aalmiramolla/ArduBot/Doc/Imágenes/img/ArduinoBT.png

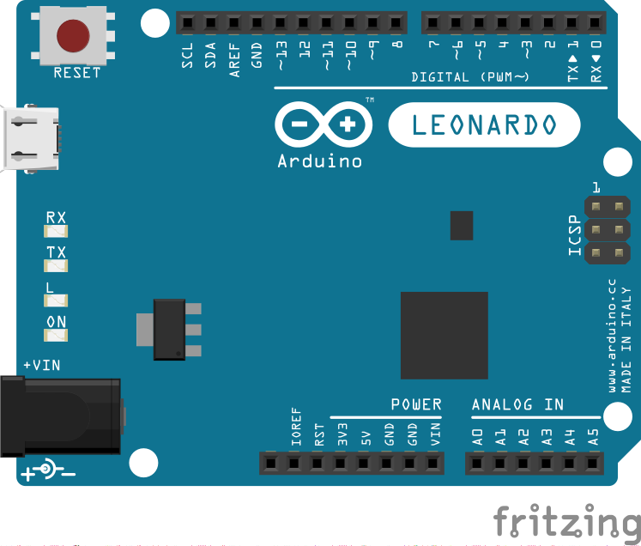
Doc/Imágenes/img/ArduinoBT.png
