aalmiramolla/ArduBot/Doc/Imágenes/img/bq.png

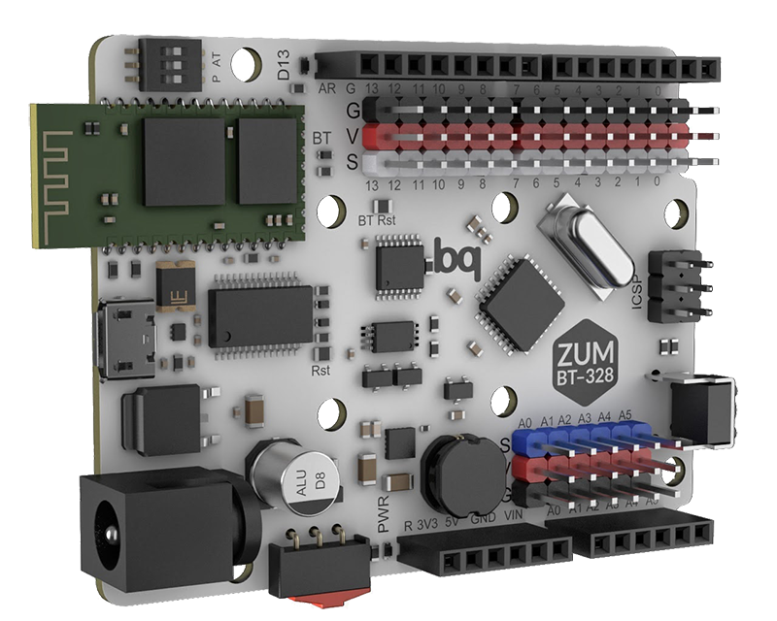
Doc/Imágenes/img/bq.png
