aalmiramolla/ArduBot/Doc/Imágenes/img/DiagramaDirectorio.png

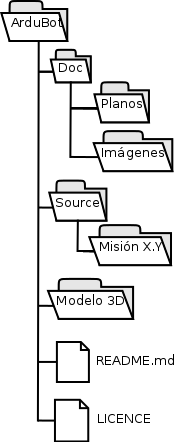
Doc/Imágenes/img/DiagramaDirectorio.png
