aalmiramolla/ArduBot/Doc/Imágenes/img/endstop.jpg

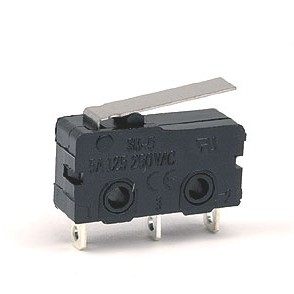
Doc/Imágenes/img/endstop.jpg
