aalmiramolla/ArduBot/Doc/Imágenes/img/endStopFunc.jpg

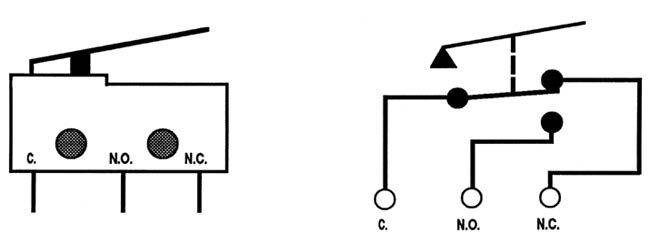
Doc/Imágenes/img/endStopFunc.jpg
