aalmiramolla/ArduBot/Doc/Imágenes/img/miniskybot.jpg

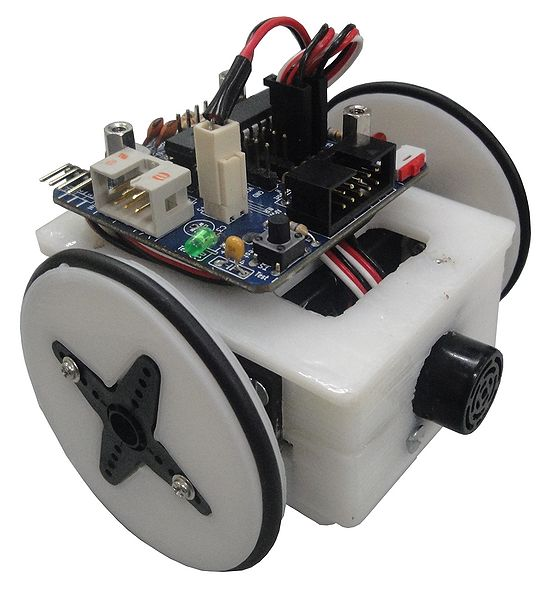
Doc/Imágenes/img/miniskybot.jpg
