aalmiramolla/ArduBot/Doc/Imágenes/img/robot_final2.jpg

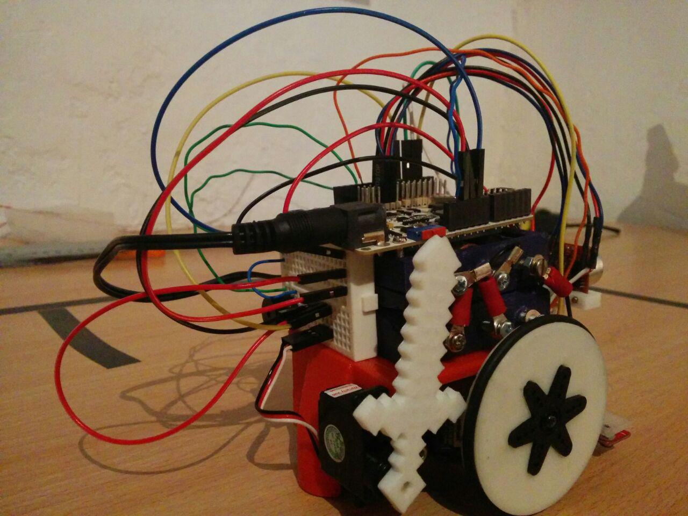
Doc/Imágenes/img/robot_final2.jpg
