aalmiramolla/ArduBot/Doc/Imágenes/img/robot_final.jpg

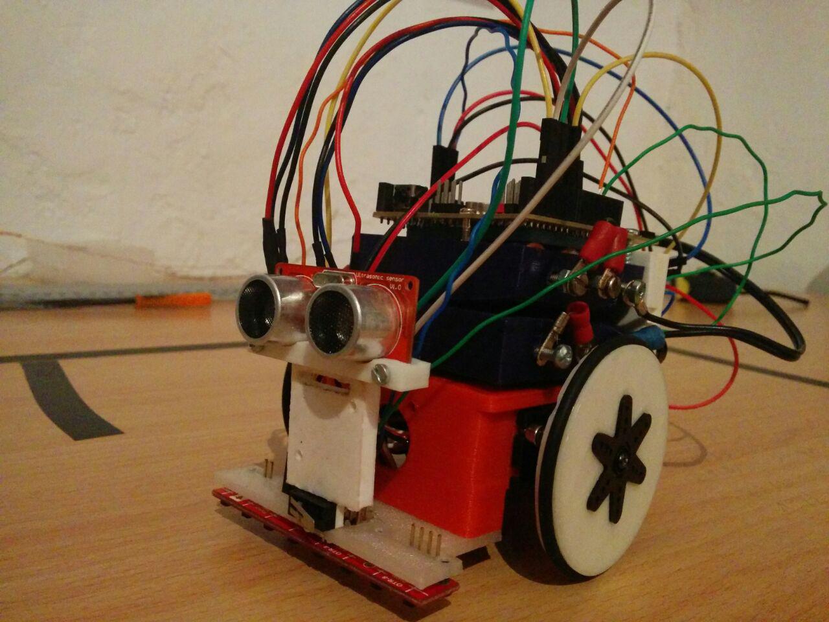
Doc/Imágenes/img/robot_final.jpg
