aalmiramolla/ArduBot/Doc/Imágenes/img/robotv1.jpg

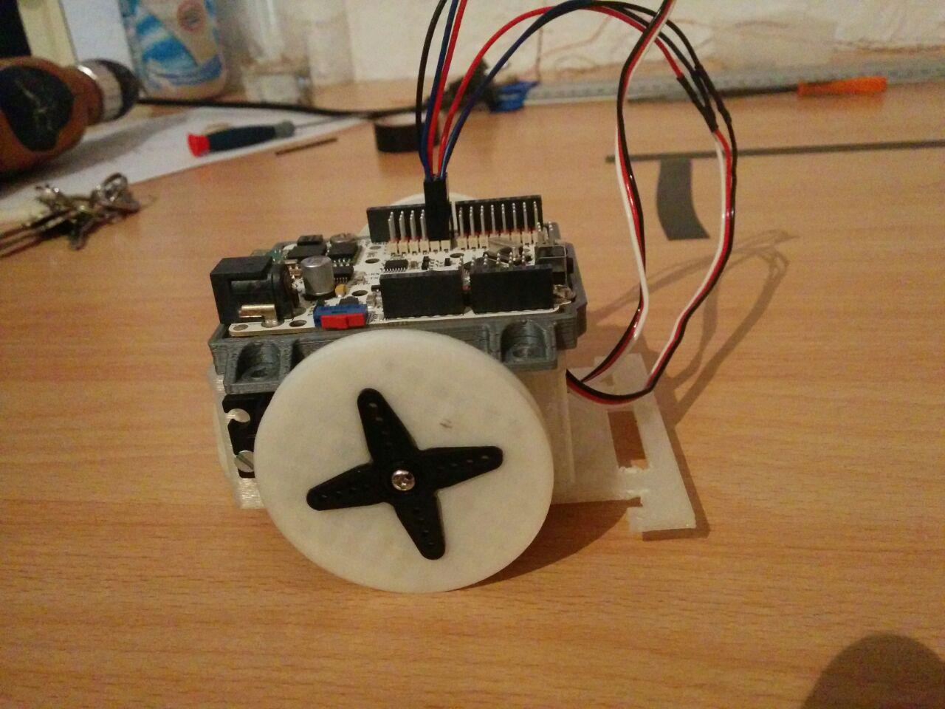
Doc/Imágenes/img/robotv1.jpg
