aalmiramolla/ArduBot/Doc/Imágenes/img/sensorluz.jpg

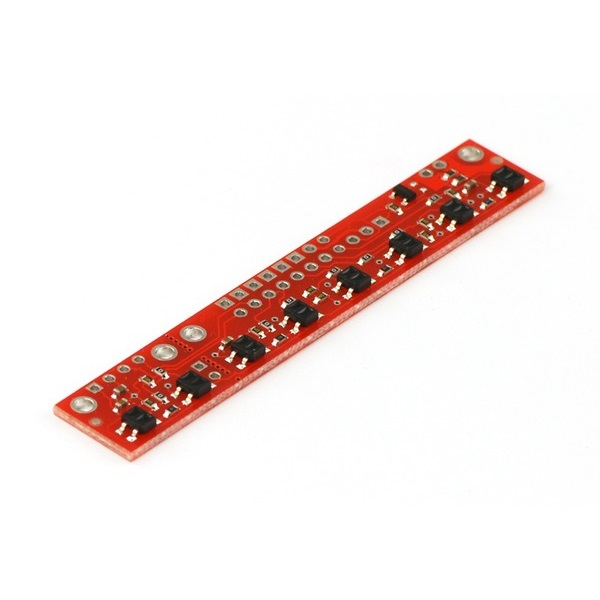
Doc/Imágenes/img/sensorluz.jpg
