aalmiramolla/ArduBot/Doc/Imágenes/img/SensorLuz.png

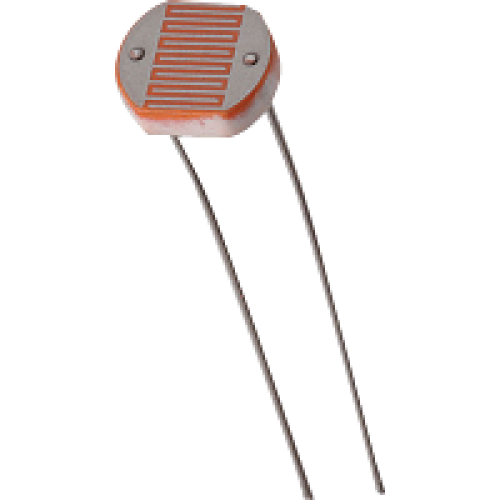
Doc/Imágenes/img/SensorLuz.png
