aalmiramolla/ArduBot/Doc/Imágenes/img/SensorReflectanciaFunc.jpg

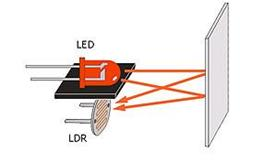
Doc/Imágenes/img/SensorReflectanciaFunc.jpg
