aalmiramolla/ArduBot/Doc/Imágenes/img/servo.jpg

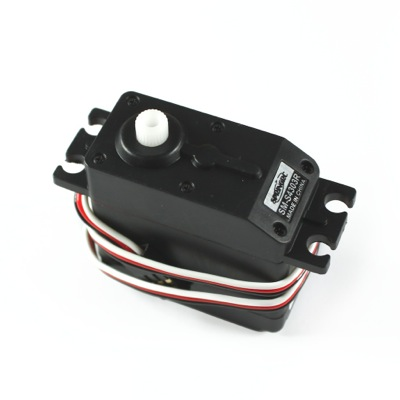
Doc/Imágenes/img/servo.jpg
