aalmiramolla/ArduBot/Doc/Imágenes/img/ServoDigital180.jpg

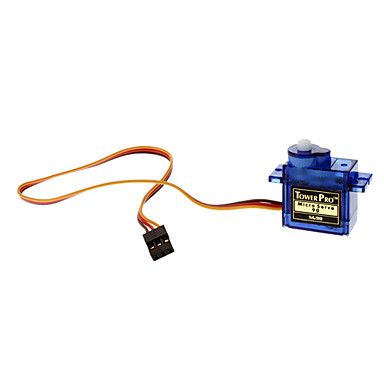
Doc/Imágenes/img/ServoDigital180.jpg
