aalmiramolla/ArduBot/Doc/Imágenes/img/sketchArduino.png

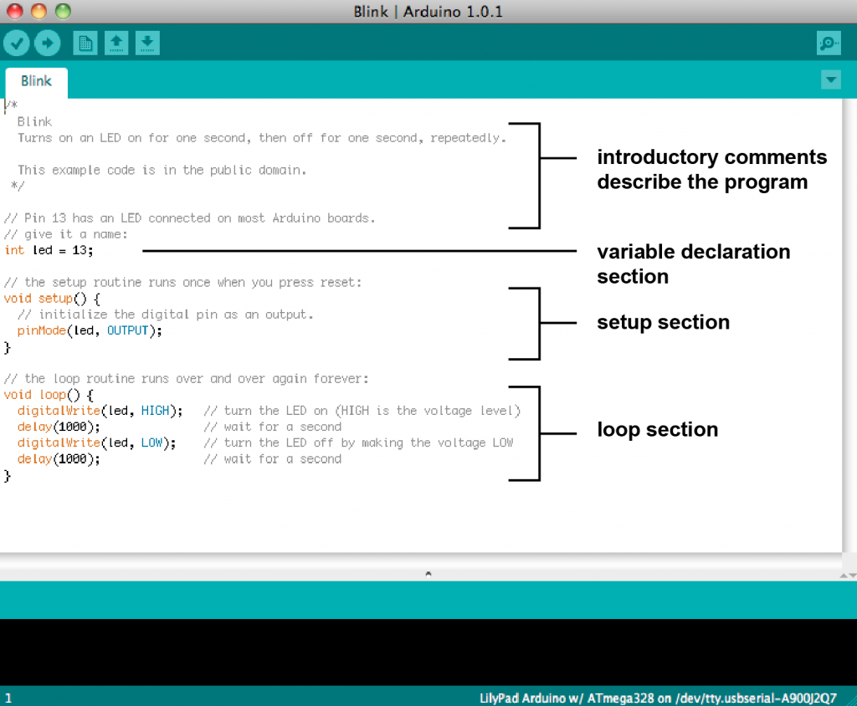
Doc/Imágenes/img/sketchArduino.png
