aalmiramolla/ArduBot/Doc/Imágenes/img/Zumbador.png

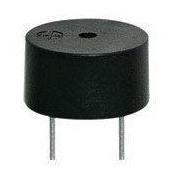
Doc/Imágenes/img/Zumbador.png
