aalmiramolla/ArduBot/Doc/Imágenes/Misiones/ImagenCirculo.png

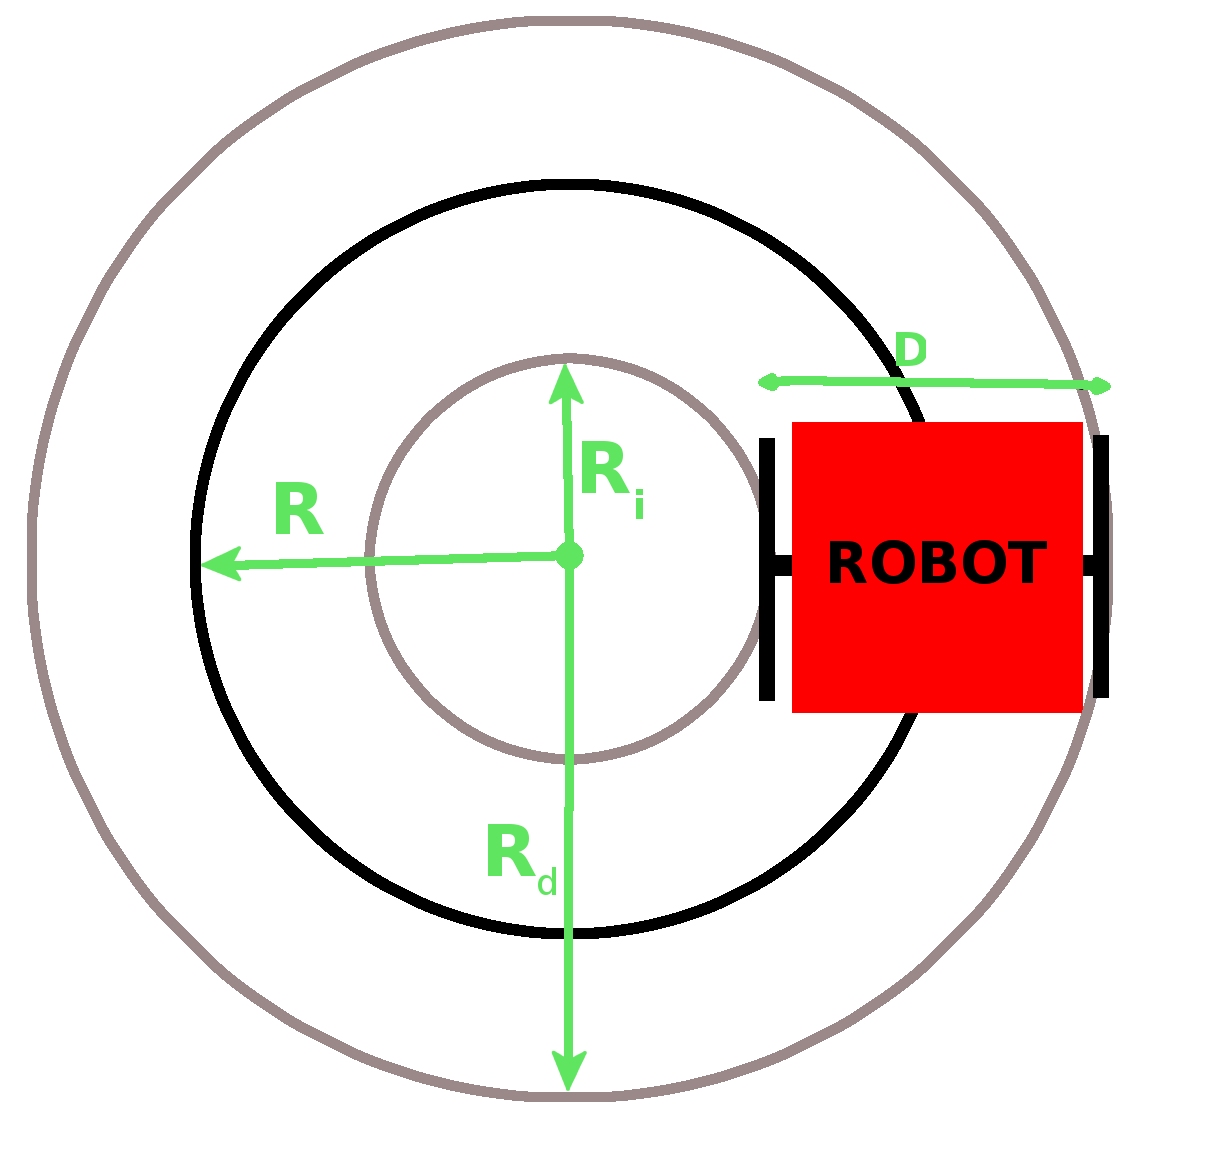
Doc/Imágenes/Misiones/ImagenCirculo.png
