aalmiramolla/ArduBot/Source/Misiones/Comunicacion/robot2.png

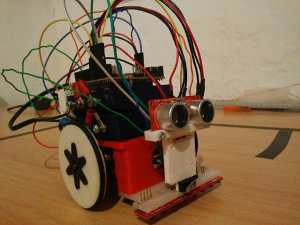
Source/Misiones/Comunicacion/robot2.png
