aalmiramolla/ArduBot/Doc/Imágenes/Montaje/MontajeUltraSonidos.jpg

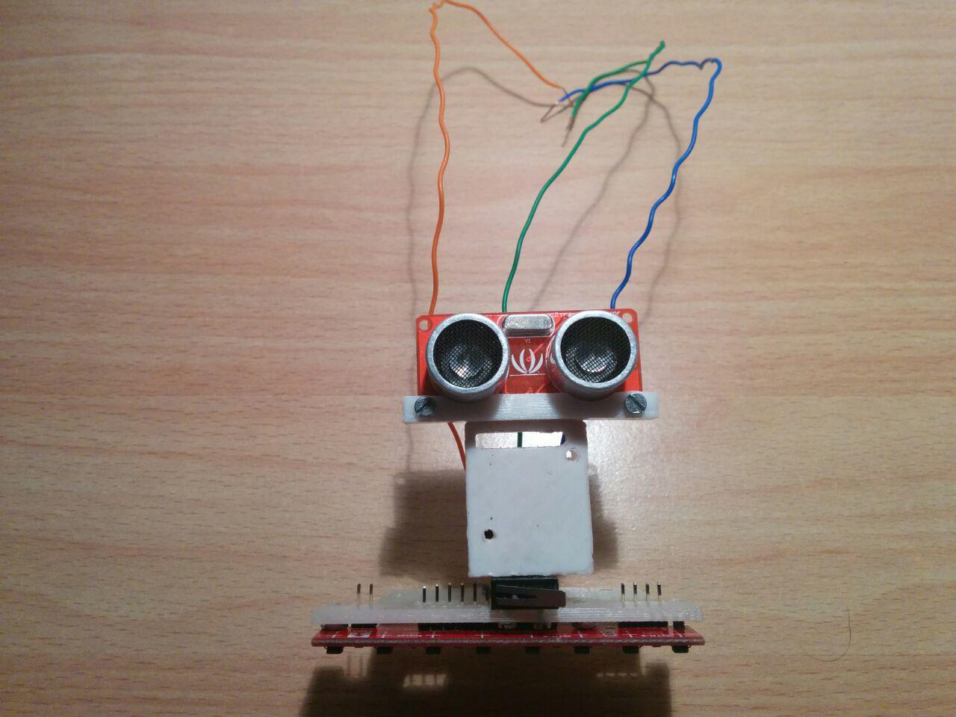
Doc/Imágenes/Montaje/MontajeUltraSonidos.jpg
