aalmiramolla/ArduBot/Doc/Imágenes/Montaje/Portapilas1.jpg

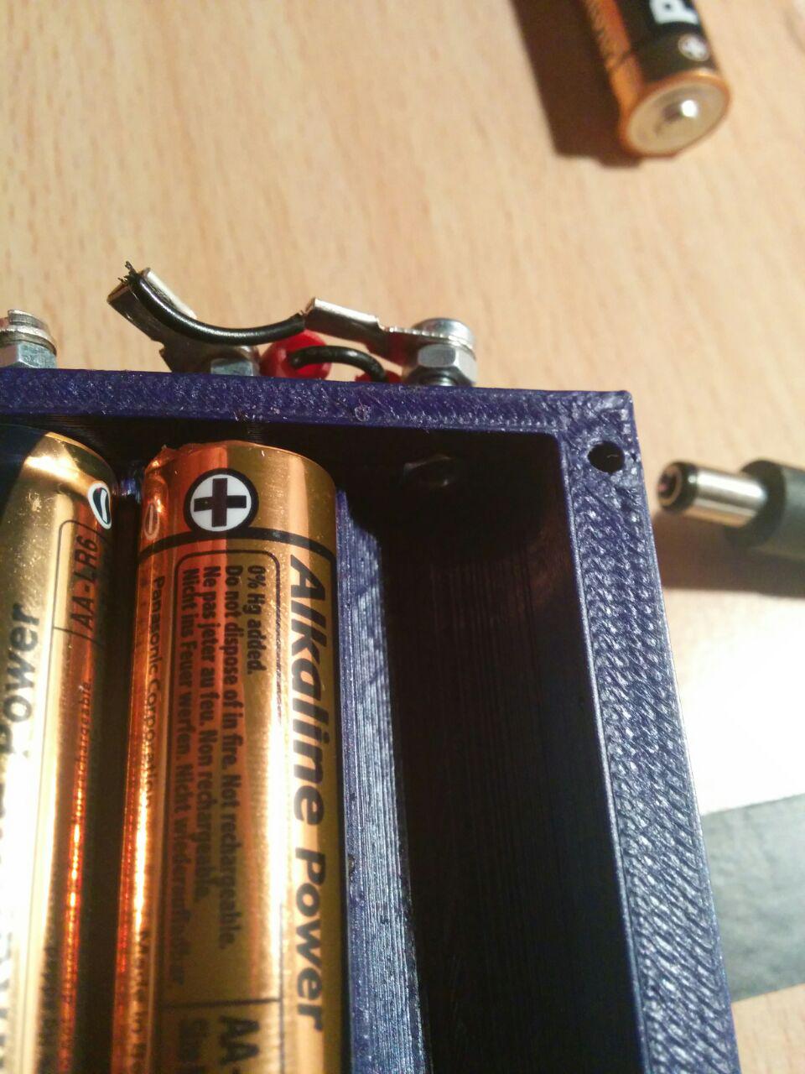
Doc/Imágenes/Montaje/Portapilas1.jpg
